jlywxy/slimarm/slimarm_classic/slarm_cls_2410/misc/截屏2023-01-17 19.11.54.png

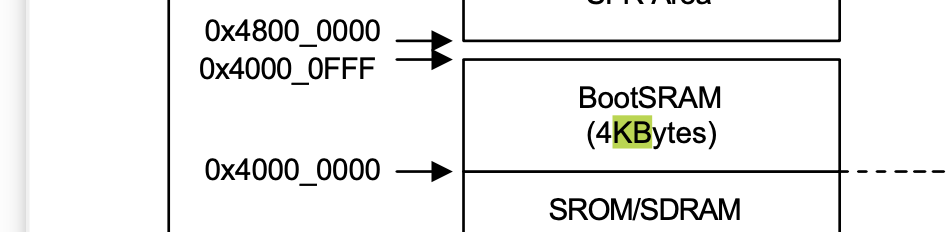
slimarm_classic/slarm_cls_2410/misc/截屏2023-01-17 19.11.54.png
