jlywxy/slimarm/slimarm_classic/slarm_cls_2410/misc/截屏2023-01-28 17.17.15.png

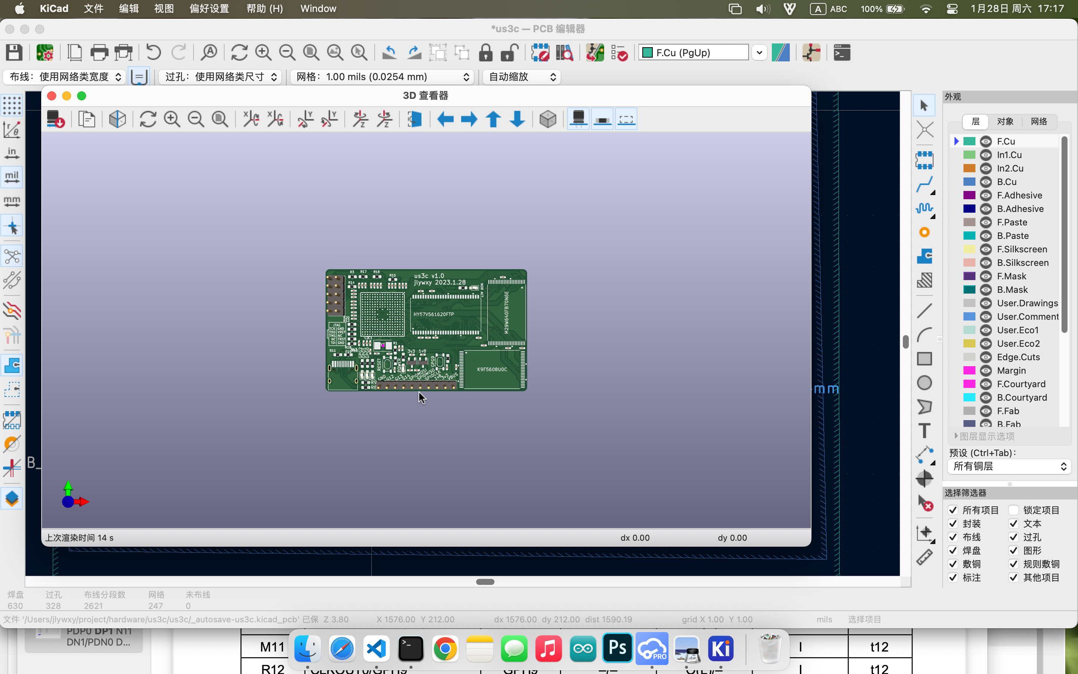
slimarm_classic/slarm_cls_2410/misc/截屏2023-01-28 17.17.15.png
