jlywxy/slimarm/slimarm_classic/slarm_cls_2410/misc/截屏2023-01-28 23.08.45.png

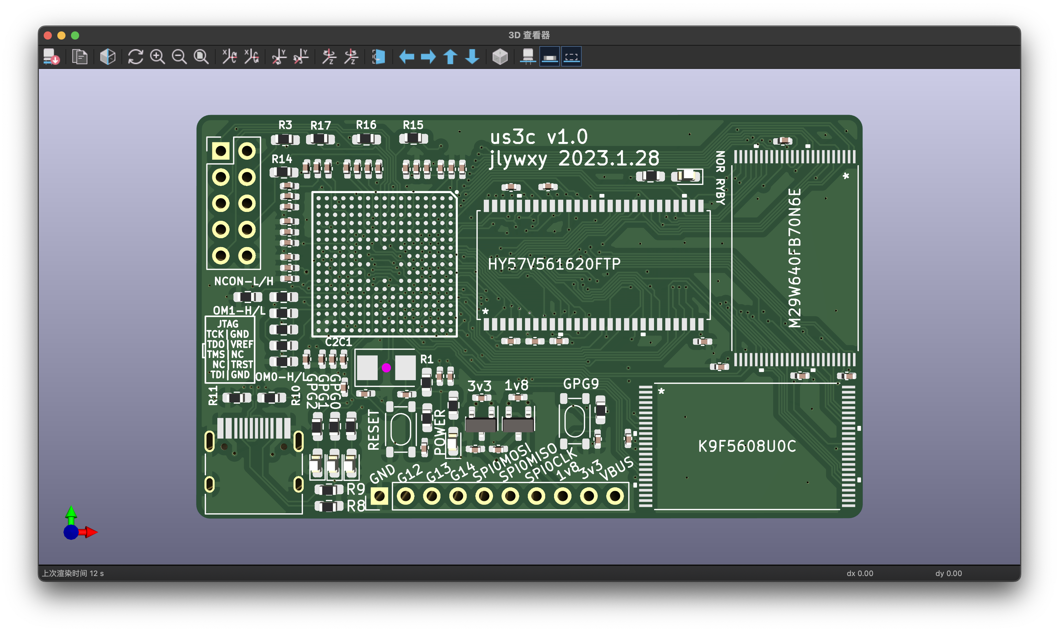
slimarm_classic/slarm_cls_2410/misc/截屏2023-01-28 23.08.45.png
