jlywxy/slimarm/slimarm_classic/slarm_cls_2410/misc/截屏2023-01-29 00.43.52.png

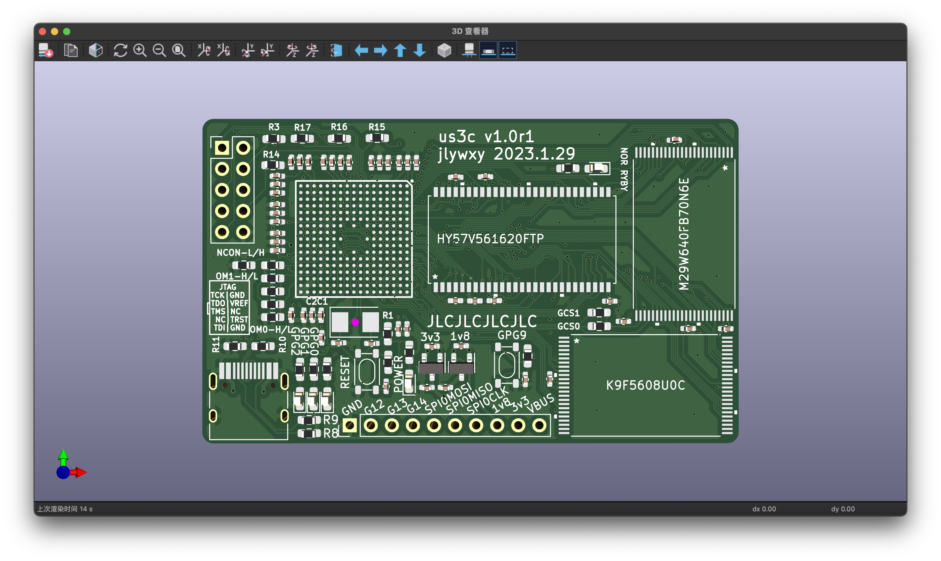
slimarm_classic/slarm_cls_2410/misc/截屏2023-01-29 00.43.52.png
