jlywxy/slimarm/slimarm_classic/slarm_cls_2410/misc/截屏2023-02-13 00.35.56.png

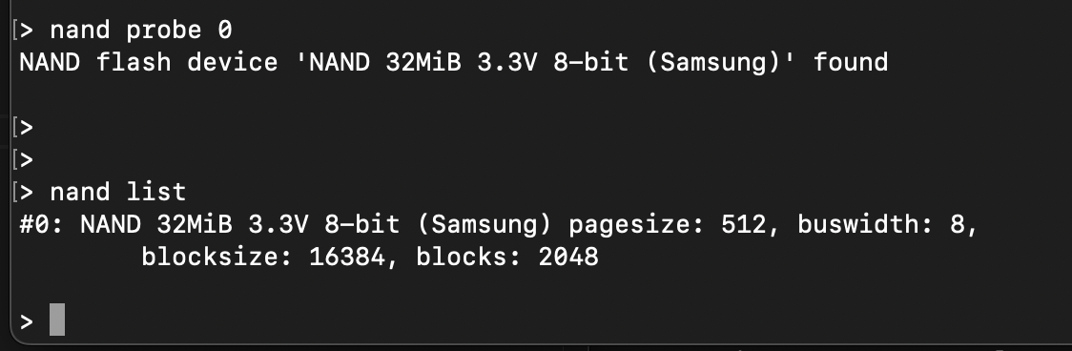
slimarm_classic/slarm_cls_2410/misc/截屏2023-02-13 00.35.56.png
